vroomfondel/micropysensorbase/micropysensorbase/ina226.py

# The MIT License (MIT)
#
# Copyright (c) 2017 Dean Miller for Adafruit Industries
# Copyright (c) 2020 Christian Becker
#
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
# THE SOFTWARE IS PROVIDED "AS IS", WITHOUT WARRANTY OF ANY KIND, EXPRESS OR
# IMPLIED, INCLUDING BUT NOT LIMITED TO THE WARRANTIES OF MERCHANTABILITY,
# FITNESS FOR A PARTICULAR PURPOSE AND NONINFRINGEMENT. IN NO EVENT SHALL THE
# AUTHORS OR COPYRIGHT HOLDERS BE LIABLE FOR ANY CLAIM, DAMAGES OR OTHER
# LIABILITY, WHETHER IN AN ACTION OF CONTRACT, TORT OR OTHERWISE, ARISING FROM,
# OUT OF OR IN CONNECTION WITH THE SOFTWARE OR THE USE OR OTHER DEALINGS IN
# THE SOFTWARE.
"""
`ina226`
====================================================

micropython driver for the INA226 current sensor.

* Author(s): Christian Becker

"""
import machine
# taken from https://github.com/robert-hh/INA219 , modified for the INA226 devices by
# Christian Becker
# June 2020

from micropython import const
# from adafruit_bus_device.i2c_device import I2CDevice

__version__ = "0.0.0-auto.0"
__repo__ = "https://github.com/elschopi/TI_INA226_micropython.git"

# Bits
# pylint: disable=bad-whitespace
_READ = const(0x01)

# Config Register (R/W)
_REG_CONFIG = const(0x00)
_CONFIG_RESET = const(0x8000)  # Reset Bit
# Constant bits - don't change
_CONFIG_CONST_BITS = const(0x4000)
# Averaging mode
_CONFIG_AVGMODE_MASK = const(0x0e00)
_CONFIG_AVGMODE_1SAMPLES = const(0x0000)
_CONFIG_AVGMODE_4SAMPLES = const(0x0200)
_CONFIG_AVGMODE_16SAMPLES = const(0x0400)
_CONFIG_AVGMODE_64SAMPLES = const(0x0600)
_CONFIG_AVGMODE_128SAMPLES = const(0x0800)
_CONFIG_AVGMODE_256SAMPLES = const(0x0a00)
_CONFIG_AVGMODE_512SAMPLES = const(0x0c00)
_CONFIG_AVGMODE_1024SAMPLES = const(0x0e00)

# Bus voltage conversion time
_CONFIG_VBUSCT_MASK = const(0x01c0)
_CONFIG_VBUSCT_140us = const(0x0000)
_CONFIG_VBUSCT_204us = const(0x0040)
_CONFIG_VBUSCT_332us = const(0x0080)
_CONFIG_VBUSCT_588us = const(0x00c0)
_CONFIG_VBUSCT_1100us = const(0x0100)
_CONFIG_VBUSCT_21116us = const(0x0140)
_CONFIG_VBUSCT_4156us = const(0x0180)
_CONFIG_AVGMODE_8244us = const(0x01c0)

# Shunt voltage conversion time
_CONFIG_VSHUNTCT_MASK = const(0x0038)
_CONFIG_VSHUNTCT_140us = const(0x0000)
_CONFIG_VSHUNTCT_204us = const(0x0008)
_CONFIG_VSHUNTCT_332us = const(0x0010)
_CONFIG_VSHUNTCT_588us = const(0x0018)
_CONFIG_VSHUNTCT_1100us = const(0x0020)
_CONFIG_VSHUNTCT_21116us = const(0x0028)
_CONFIG_VSHUNTCT_4156us = const(0x0030)
_CONFIG_VSHUNTCT_8244us = const(0x0038)

# Operating mode
_CONFIG_MODE_MASK = const(0x0007)  # Operating Mode Mask
_CONFIG_MODE_POWERDOWN = const(0x0000)
_CONFIG_MODE_SVOLT_TRIGGERED = const(0x0001)
_CONFIG_MODE_BVOLT_TRIGGERED = const(0x0002)
_CONFIG_MODE_SANDBVOLT_TRIGGERED = const(0x0003)
_CONFIG_MODE_ADCOFF = const(0x0004)
_CONFIG_MODE_SVOLT_CONTINUOUS = const(0x0005)
_CONFIG_MODE_BVOLT_CONTINUOUS = const(0x0006)
_CONFIG_MODE_SANDBVOLT_CONTINUOUS = const(0x0007)

# SHUNT VOLTAGE REGISTER (R)
_REG_SHUNTVOLTAGE = const(0x01)

# BUS VOLTAGE REGISTER (R)
_REG_BUSVOLTAGE = const(0x02)

# POWER REGISTER (R)
_REG_POWER = const(0x03)

# CURRENT REGISTER (R)
_REG_CURRENT = const(0x04)

# CALIBRATION REGISTER (R/W)
_REG_CALIBRATION = const(0x05)
# pylint: enable=bad-whitespace


def _to_signed(num: int) -> int:
    if num > 0x7FFF:
        num -= 0x10000
    return num


class INA226:
    """Driver for the INA226 current sensor"""
    def __init__(self, i2c_device: machine.I2C|machine.SoftI2C, addr: int = 0x40) -> None:
        self.i2c_device: machine.I2C|machine.SoftI2C = i2c_device

        self.i2c_addr: int = addr
        self.buf: bytearray = bytearray(2)
        # Multiplier in mA used to determine current from raw reading
        self._current_lsb: float = 0
        # Multiplier in W used to determine power from raw reading
        self._power_lsb: float = 0

        # Set chip to known config values to start
        self._cal_value = 4096
        self.set_calibration()

    def _write_register(self, reg: int, value: int) -> None:
        self.buf[0] = (value >> 8) & 0xFF
        self.buf[1] = value & 0xFF
        self.i2c_device.writeto_mem(self.i2c_addr, reg, self.buf)

    def _read_register(self, reg: int) -> int:
        self.i2c_device.readfrom_mem_into(self.i2c_addr, reg & 0xff, self.buf)
        value = (self.buf[0] << 8) | (self.buf[1])
        return value

    @property
    def shunt_voltage(self) -> float:
        """The shunt voltage (between V+ and V-) in Volts (so +-.327V)"""
        value = _to_signed(self._read_register(_REG_SHUNTVOLTAGE))
        # The least signficant bit is 10uV which is 0.00001 volts
        return value * 0.00001

    @property
    def bus_voltage(self) -> float:
        """The bus voltage (between V- and GND) in Volts"""
        raw_voltage = self._read_register(_REG_BUSVOLTAGE)
        # voltage in millVolt is register content multiplied with 1.25mV/bit
        voltage_mv = raw_voltage * 1.25
        # Return Volts instead of milliVolts
        return voltage_mv * 0.001

    @property
    def current(self) -> float:
        """The current through the shunt resistor in milliamps."""
        # Sometimes a sharp load will reset the INA219, which will
        # reset the cal register, meaning CURRENT and POWER will
        # not be available ... athis by always setting a cal
        # value even if it's an unfortunate extra step
        self._write_register(_REG_CALIBRATION, self._cal_value)

        # Now we can safely read the CURRENT register!
        raw_current = _to_signed(self._read_register(_REG_CURRENT))
        return raw_current * self._current_lsb
    
    @property
    def power(self) -> float:
        # INA226 stores the calculated power in this register        
        raw_power = _to_signed(self._read_register(_REG_POWER))
        # Calculated power is derived by multiplying raw power value with the power LSB
        return raw_power * self._power_lsb
# Example calculations for calibration register value, current LSB and power LSB
# 1. Assuming a 100milliOhm resistor as shunt
# RSHUNT = 0.1
#
# 2. Determine current_lsb
# Assuming a maximum expected current of 3.6A
# current_lsb = MaxExpected_I / (2^15)
# current_lsb = 3.6A / (2^15)
# current_lsb = 0.0001098632813
# -> Rounding to "nicer" numbers:
# current_lsb = 0.0001
#
# 3. Setting the power LSB
# power_lsb = 25 * current_lsb
# power_lsb = 25 * 0.0001
# power_lsb = 0.0025
#
# 4. Determine calibration register value
# cal_value = 0.00512 / (RSHUNT * current_lsb)
# cal_value = 0.00512 / (0.1 * 0.0001)
# cal_value = 512
#
#
    def set_calibration(self) -> None:  # pylint: disable=invalid-name
        """Configures to INA226 to be able to measure up to 36V and 2A
            of current. Counter overflow occurs at 3.2A.
           ..note :: These calculations assume a 0.1 shunt ohm resistor"""
        self._current_lsb = .0001
        self._cal_value = 512
        self._power_lsb = .0025  
        self._write_register(_REG_CALIBRATION, self._cal_value)
        
        config = (_CONFIG_CONST_BITS |
                  _CONFIG_AVGMODE_512SAMPLES |
                  _CONFIG_VBUSCT_588us |
                  _CONFIG_VSHUNTCT_588us |
                  _CONFIG_MODE_SANDBVOLT_CONTINUOUS)
        
        self._write_register(_REG_CONFIG, config)


    # https://docs.google.com/spreadsheets/d/1k0MbBsduRgoQ8huFrBwaHQnYhl97LjkpEw-sIXykTEg/edit?pli=1#gid=0
    # 0,0001
    # 0,0025
    # 512
    def set_calibration_custom(self, calValue: int = 512, config: int = 0x4127) -> None:
    # Set the configuration register externally by using the hex value for the config register
    # Value can be calculated with spreadsheet
    # Calibration value needs to be calculated seperately and passed as parameter too
        self._cal_value = calValue        
        self._write_register(_REG_CALIBRATION, self._cal_value)
        self._write_register(_REG_CONFIG, config)
