vroomfondel/micropysensorbase/micropysensorbase/boot.py

# This file is executed on every boot (including wake-boot from deepsleep)
#import esp
#esp.osdebug(None)

# battery-voltage-check
# https://www.youtube.com/watch?v=5JIJO1swQPE
# https://www.xtronical.com/

# https://docs.micropython.org/en/latest/library/machine.html
# machine.reset()
#Resets the device in a manner similar to pushing the external RESET button.

#machine.soft_reset()
#Performs a soft reset of the interpreter, deleting all Python objects and resetting the Python heap. It tries to retain the method by which the user is connected to the MicroPython REPL (eg #serial, USB, Wifi).

# CHECK: https://github.com/micropython/micropython-lib?tab=readme-ov-file

# replace time.localtime() system-wide:
# https://github.com/orgs/micropython/discussions/11173
# https://docs.micropython.org/en/latest/library/index.html#extending-built-in-libraries-from-python

# mip install modules!
# https://github.com/micropython/micropython-lib

from . import config


from . import logging, time
logger = logging.get_logger(__name__)
logger.setLevel(logging.DEBUG)

if __name__ in config.get_config_data_dict(config.data, "loglevel"):
    melv: int|None = logging.get_log_level_by_name(
        config.get_config_data_str(config.get_config_data_dict(config.data, "loglevel"), "boot"))
    if melv is not None:
        logger.setLevel(melv)


if "boot_ssd" in config.data and config.get_config_data_bool(config.data, "boot_ssd"):
    try:
        from . import boot_ssd
        boot_ssd.setup()
    except Exception as ex:
        import sys
        import io

        _out = io.StringIO()
        sys.print_exception(ex)
        sys.print_exception(ex, _out)

        logger.error(_out.getvalue())
        time.sleep(2)  # type: ignore


import sys
import io

if not config.DISABLE_INET:
    from . import wifi
    wifi.ensure_wifi()
    wifi.start_web_repl()

    try:
        import ntptime

        gwntp = None

        if config.INTVERSION >= 124:
            gwntp = wifi.wlan.ipconfig("gw4")
        else:
            gwntp = wifi.wlan.ifconfig()[2]

        poolntp = "pool.ntp.org"
        ntptime.timeout = 2

        for i in range(10):
            for h in  [gwntp, poolntp]:
                try:
                    ntptime.host = h
                    ntptime.settime()
                    time.set_had_proper_time_set(True)
                    logger.info(f"ntptime set by host {h}")
                    break
                except Exception as ex:
                    _out = io.StringIO()
                    sys.print_exception(ex)
                    sys.print_exception(ex, _out)

                    logger.error(_out.getvalue())
                    time.sleep(2)  # type: ignore

            if time.get_had_proper_time_set():
                break
    except Exception as imex:
        _out = io.StringIO()
        sys.print_exception(imex)
        sys.print_exception(imex, _out)

        logger.error(_out.getvalue())
else:
    logger.info("INET DISABLED... NO NTPTIME ETC...")

from . import meminfo
meminfo.main()

# https://forum.micropython.org/viewtopic.php?f=2&t=4034
# # Micropython esp8266
# # This code returns the Central European Time (CET) including daylight saving
# # Winter (CET) is UTC+1H Summer (CEST) is UTC+2H
# # Changes happen last Sundays of March (CEST) and October (CET) at 01:00 UTC
# # Ref. formulas : http://www.webexhibits.org/daylightsaving/i.html
# #                 Since 1996, valid through 2099
#
# import utime

# def get_cet_timeoffset() -> int:
#     year = utime.localtime()[0]       #get current year
#     HHMarch   = utime.mktime((year, 3, (31-(int(5*year/4+4)) % 7), 1, 0, 0, 0, 0)) #Time of March change to CEST  # (year, month, mday, hour, minute, second, weekday, yearday)
#     HHOctober = utime.mktime((year, 10, (31-(int(5*year/4+1)) % 7), 2, 0, 0, 0, 0)) #Time of October change to CET # (year, month, mday, hour, minute, second, weekday, yearday)
#     now = utime.time()
#     if now < HHMarch:               # we are before last sunday of march
#         return 3600  # CET:  UTC+1H
#     elif now < HHOctober:           # we are before last sunday of october
#         return 7200  # CEST: UTC+2H
#     else:                            # we are after last sunday of october
#         return 3600  # CET:  UTC+1H
#
# # https://github.com/micropython/micropython-lib
#
# cettimeoffsetseconds = get_cet_timeoffset()
#
# print(f"{cettimeoffsetseconds=}")

# ntptime.NTP_DELTA -= cettimeoffsetseconds
# ntptime.settime()  # reset with correct timezone | needed first call to detect month

# boottime = utime.time()
# print("boot.py :: local_boottime: ", utime.localtime(boottime))
# print("boot.py :: utime.time(): ", boottime)

import machine
rc = machine.reset_cause()

if rc == machine.PWRON_RESET:
    logger.info("RESET CAUSE :: PWRON_RESET")

if rc == machine.HARD_RESET:
    logger.info("RESET CAUSE :: HARD_RESET")

if rc == machine.WDT_RESET:
    logger.info("RESET CAUSE :: WDT_RESET")

if rc == machine.DEEPSLEEP_RESET:
    logger.info("RESET CAUSE :: DEEPSLEEP_RESET")

if rc == machine.SOFT_RESET:
    logger.info("RESET CAUSE :: SOFT_RESET")

# import micropython
# micropython.alloc_emergency_exception_buf(100)

logger.info("BOOT DONE")

logger.info("you could update me by issuing these commands:\n"
            "import mip\n\n"
            "mip.install(\"https://raw.githubusercontent.com/vroomfondel/micropysensorbase/main/package.json\")\n\tbzw.\n"
            "mip.install(\"github:vroomfondel/micropysensorbase\")\n\n")

# do not forget to enable/start this afterwards in your own boot.py/main.py

logger.info("or even better (after having set up something like this locally: https://github.com/vroomfondel/mipserver)\n"
            "import mip\nfrom micropysensorbase import config\n\n"
            "mip.install(\"micropysensorbase\", index=config.get_config_data_str(config.data, \"mip_index\"))\n"
            "\tthus installing/updating from a local github-proxy-on-the-fly-mpy-compiler-thingy...")

# import mip
# from micropysensorbase import config
# mip.install("micropysensorbase", index=config.get_config_data_str(config.data, "mip_index"))


# the next two lines take the "activation" from my github and overwrites whatever boot.py and main.py is currently present on the MCU
# mpremote mip install --target / github:vroomfondel/micropysensorbase/boot.py
# mpremote mip install --target / github:vroomfondel/micropysensorbase/main.py

# mpremote mip install github:vroomfondel/micropysensorbase

#import ssl
#ssl._create_default_context = lambda: ssl.SSLContext(ssl.PROTOCOL_TLS_CLIENT)

#import mip
# mip.install("https://raw.githubusercontent.com/vroomfondel/micropysensorbase/main/package.json", mpy=True, target="/")
#mip.install("github:vroomfondel/micropysensorbase/main.py", mpy=False, target="/")
#  mip.install("github:vroomfondel/micropysensorbase", mpy=True, target="/")
# -> kriege ich protocol error...
# mip.install("https://raw.githubusercontent.com/vroomfondel/micropysensorbase/main/package.json")

# mpremote mip install "github:vroomfondel/micropysensorbase
# mpremote mip install github:vroomfondel/micropysensorbase
